Domochip/WPalaSensor/src/base/CrashSaver.cpp

#include "CrashSaver.h"
#include "../Main.h" // for VERSION_NUMBER and CUSTOM_APP_MODEL

#ifdef ESP8266

extern "C" void custom_crash_callback(struct rst_info *rst_info, uint32_t stack, uint32_t stack_end)
{
    // avoid to log a crash during Update reboot
    if (SystemState::shouldReboot)
        return;

    if (CrashSaver::_fs == nullptr)
        return;

    FS &fs = *CrashSaver::_fs;

    uint32_t crashTime = millis();

    // open the file in appending mode
    File logFile = fs.open(CrashSaver::getNextLogFilePath(), "a");

    // if the file does not yet exist
    if (!logFile)
    {
        // open the file in write mode
        logFile = fs.open(CrashSaver::getNextLogFilePath(), "w");
    }

    if (!logFile)
        return;

    // if the file is (now) a valid file

    // maximum tmpBuffer size needed is 93 (UTC datetime crash line), so 100 should be enough
    char tmpBuffer[100];

    // log model and version info
    int writtenLen = snprintf_P(tmpBuffer, sizeof(tmpBuffer), PSTR("Model: %s\nVersion: %s\n"), CUSTOM_APP_MODEL, VERSION_NUMBER);
    if (writtenLen > 0)
        logFile.write(tmpBuffer, writtenLen);

    // log crash time, reason and exception cause
    if (CrashSaver::_ntpEpoch != 0)
    {
        time_t crashEpoch = (time_t)(CrashSaver::_ntpEpoch + (crashTime - CrashSaver::_ntpMillis) / 1000);
        struct tm tmInfo;
        gmtime_r(&crashEpoch, &tmInfo);
        sprintf_P(tmpBuffer, PSTR("Crashed at %04d-%02d-%02d %02d:%02d:%02d UTC\nRestart reason: %d\nException cause: %d\n"),
                  tmInfo.tm_year + 1900, tmInfo.tm_mon + 1, tmInfo.tm_mday,
                  tmInfo.tm_hour, tmInfo.tm_min, tmInfo.tm_sec,
                  rst_info->reason, rst_info->exccause);
    }
    else
        sprintf_P(tmpBuffer, PSTR("Crashed at %lu ms (no NTP)\nRestart reason: %d\nException cause: %d\n"), crashTime, rst_info->reason, rst_info->exccause);

    logFile.write(tmpBuffer, strlen(tmpBuffer));

    // log crash info (epc1, epc2, epc3, excvaddr, depc) and stack trace
    // 83 chars of epc1, epc2, epc3, excvaddr, depc info + 13 chars of >stack>
    sprintf_P(tmpBuffer, PSTR("epc1=0x%08x epc2=0x%08x epc3=0x%08x excvaddr=0x%08x depc=0x%08x\n>>>stack>>>\n"),
              rst_info->epc1, rst_info->epc2, rst_info->epc3, rst_info->excvaddr, rst_info->depc);
    logFile.write(tmpBuffer, strlen(tmpBuffer));

    uint16_t stackLength = stack_end - stack;

    // log stack trace
    // one loop contains 45 chars of stack address and its content
    // e.g. "3fffffb0: feefeffe feefeffe 3ffe8508 40100459"
    for (uint16_t i = 0; i < stackLength; i += 0x10)
    {
        uint32_t *p0 = (uint32_t *)(stack + i + 0);
        uint32_t *p1 = (uint32_t *)(stack + i + 4);
        uint32_t *p2 = (uint32_t *)(stack + i + 8);
        uint32_t *p3 = (uint32_t *)(stack + i + 12);

        writtenLen = snprintf_P(tmpBuffer, sizeof(tmpBuffer), PSTR("%08x: %08x %08x %08x %08x\n"), stack + i, *p0, *p1, *p2, *p3);

        if (writtenLen > 0)
            logFile.write(tmpBuffer, writtenLen);
    }
    logFile.write("<<<stack<<<\n\n");
    logFile.close();
}

FS *CrashSaver::_fs = nullptr;
uint32_t CrashSaver::_ntpEpoch = 0;
uint32_t CrashSaver::_ntpMillis = 0;

char CrashSaver::_nextLogFilePath[LOG_FILE_PATH_LEN] = {0};

void CrashSaver::init(FS &fs, const char *ntpServer /* = "pool.ntp.org" */)
{
    _fs = &fs;
    configTime(0, 0, ntpServer);
    settimeofday_cb([]()
                    {
        time_t t = time(nullptr);
        if (t > 1000000000UL)
        {
            _ntpEpoch = (uint32_t)t;
            _ntpMillis = millis();
        } });
    calculateNextLogFilePath();
}

void CrashSaver::calculateNextLogFilePath()
{
    uint16_t nextFileIndex = count();
    if (nextFileIndex < UINT16_MAX)
        nextFileIndex++;

    snprintf(_nextLogFilePath, sizeof(_nextLogFilePath), "%s%u", DEFAULT_DIR, nextFileIndex);
}

uint16_t CrashSaver::count()
{
    if (_fs == nullptr)
        return 0;

    uint16_t fileCount = 0;
    Dir dir = _fs->openDir(DEFAULT_DIR);
    while (dir.next())
    {
        if (fileCount < UINT16_MAX)
            fileCount++;
    }

    return fileCount;
}

void CrashSaver::iterateCrashLogFiles(std::function<void(uint16_t, const char *)> callback)
{
    if (_fs == nullptr || !callback)
        return;

    Dir dir = _fs->openDir(DEFAULT_DIR);
    uint16_t fileNumber = 0;
    while (dir.next())
    {
        if (fileNumber < UINT16_MAX)
            fileNumber++;

        char fullPath[LOG_FILE_PATH_LEN] = {0};
        strncpy(fullPath, DEFAULT_DIR, sizeof(fullPath) - 1);
        strncat(fullPath, dir.fileName().c_str(), sizeof(fullPath) - strlen(fullPath) - 1);

        callback(fileNumber, fullPath);
        yield();
    }
}

bool CrashSaver::clearAllLogs()
{
    if (_fs == nullptr)
        return false;

    bool allRemoved = true;
    Dir dir = _fs->openDir(DEFAULT_DIR);
    while (dir.next())
    {
        char fullPath[LOG_FILE_PATH_LEN] = {0};
        strncpy(fullPath, DEFAULT_DIR, sizeof(fullPath) - 1);
        strncat(fullPath, dir.fileName().c_str(), sizeof(fullPath) - strlen(fullPath) - 1);

        if (!_fs->remove(fullPath))
            allRemoved = false;
    }

    calculateNextLogFilePath();

    return allRemoved;
}

#endif // ESP8266
